katzcreates/Clean-Air-Necklace/3D Models/STLs/CleanAirNecklace_V2_ClearCoverChannel05.stl

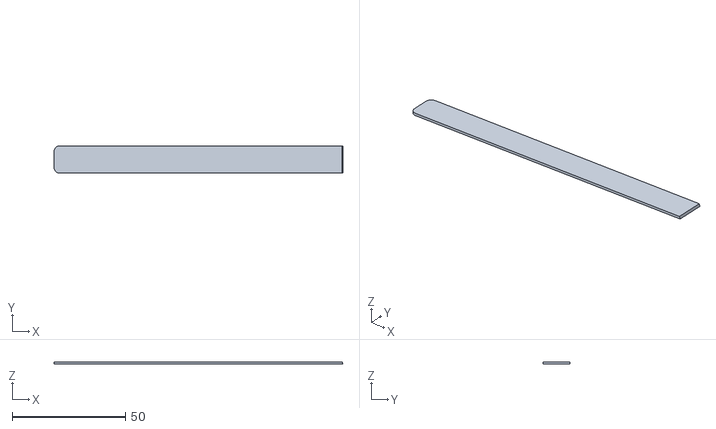
[picture p15: CAD file, 2023-09-17]
3D Models/STLs/CleanAirNecklace_V2_ClearCoverChannel05.stl
127.4 x 12.0 x 1.00
