katzcreates/Clean-Air-Necklace/3D Models/STLs/CleanAirNecklace_V2_ClearCoverChannel02.stl

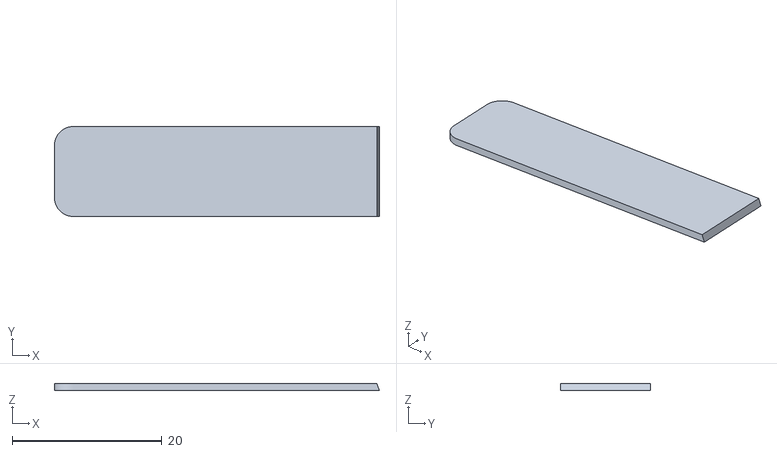
[picture p16: CAD file, 2023-09-17]
3D Models/STLs/CleanAirNecklace_V2_ClearCoverChannel02.stl
43.4 x 12.0 x 1.00
