katzcreates/Clean-Air-Necklace/3D Models/STLs/CleanAirNecklace_V2_LEDChannel01.stl

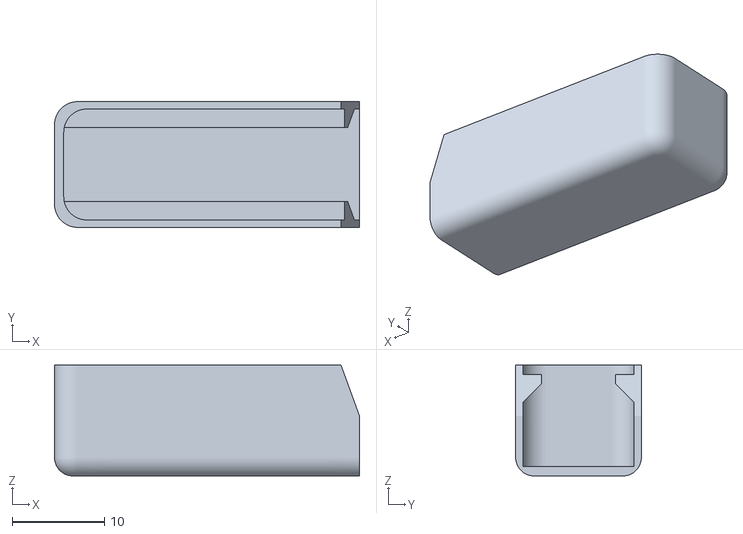
[picture p17: CAD file, 2023-09-17]
3D Models/STLs/CleanAirNecklace_V2_LEDChannel01.stl
33.0 x 13.6 x 12.0
