katzcreates/Clean-Air-Necklace/3D Models/STLs/CleanAirNecklace_V2_ClearCoverChannel03.stl

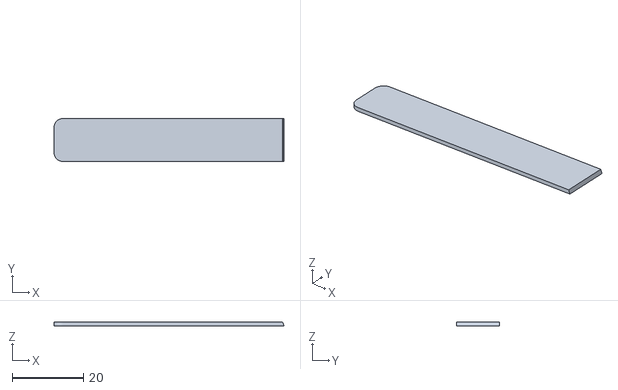
[picture p18: CAD file, 2023-09-17]
3D Models/STLs/CleanAirNecklace_V2_ClearCoverChannel03.stl
64.4 x 12.0 x 1.00
