katzcreates/Clean-Air-Necklace/3D Models/STLs/CleanAirNecklace_V2_ClearCoverChannel08.stl

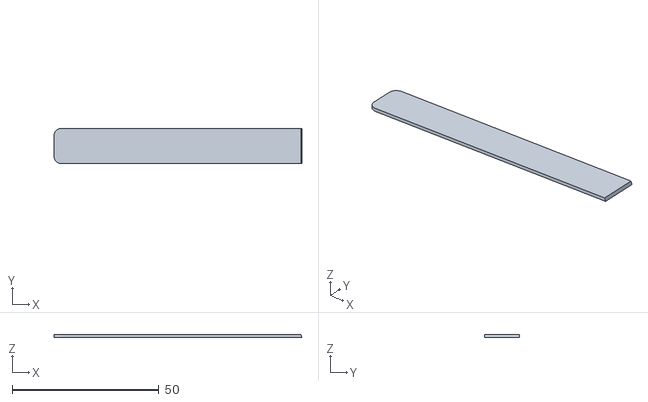
[picture p19: CAD file, 2023-09-17]
3D Models/STLs/CleanAirNecklace_V2_ClearCoverChannel08.stl
84.4 x 12.0 x 1.00
