katzcreates/Clean-Air-Necklace/3D Models/STLs/CleanAirNecklace_V2_LEDChannel08.stl

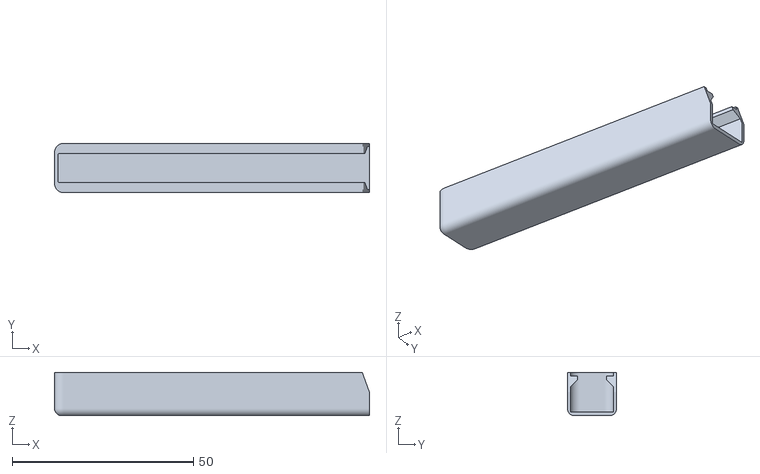
[picture p20: CAD file, 2023-09-17]
3D Models/STLs/CleanAirNecklace_V2_LEDChannel08.stl
87.0 x 13.6 x 12.0
