katzcreates/Clean-Air-Necklace/3D Models/STLs/CleanAirNecklace_V2_LEDChannel07.stl

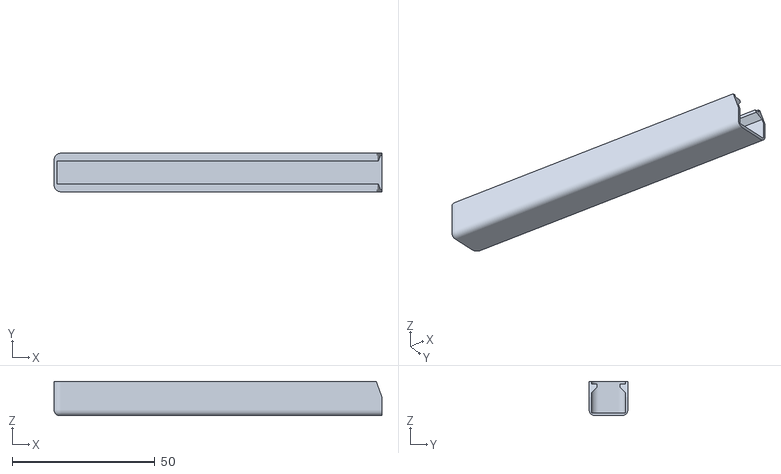
[picture p21: CAD file, 2023-09-17]
3D Models/STLs/CleanAirNecklace_V2_LEDChannel07.stl
115.0 x 13.6 x 12.0
