katzcreates/Clean-Air-Necklace/3D Models/STLs/CleanAirNecklace_V2_LEDChannel05.stl

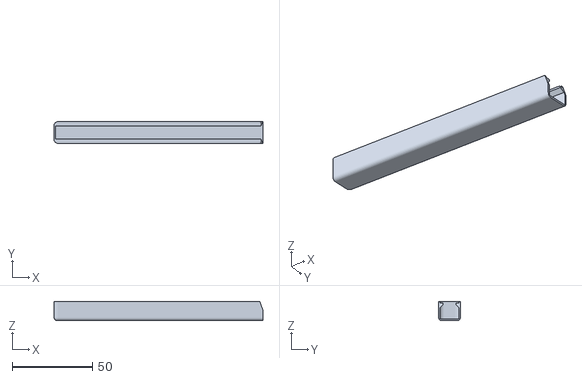
[picture p22: CAD file, 2023-09-17]
3D Models/STLs/CleanAirNecklace_V2_LEDChannel05.stl
130.0 x 13.6 x 12.0
