katzcreates/Clean-Air-Necklace/3D Models/STLs/CleanAirNecklace_V2_ClearCoverChannel06.stl

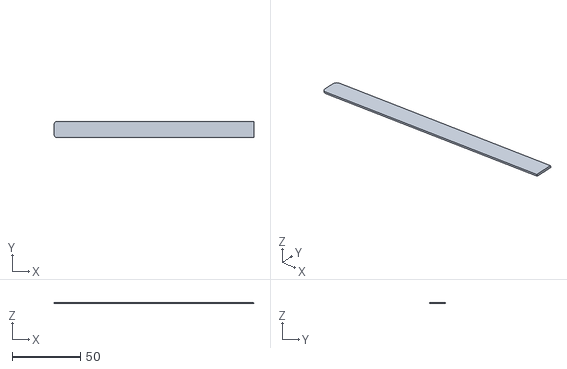
[picture p23: CAD file, 2023-09-17]
3D Models/STLs/CleanAirNecklace_V2_ClearCoverChannel06.stl
146.4 x 12.0 x 1.00
