katzcreates/Clean-Air-Necklace/3D Models/STLs/CleanAirNecklace_V2_MCUEnclosureDrop.stl

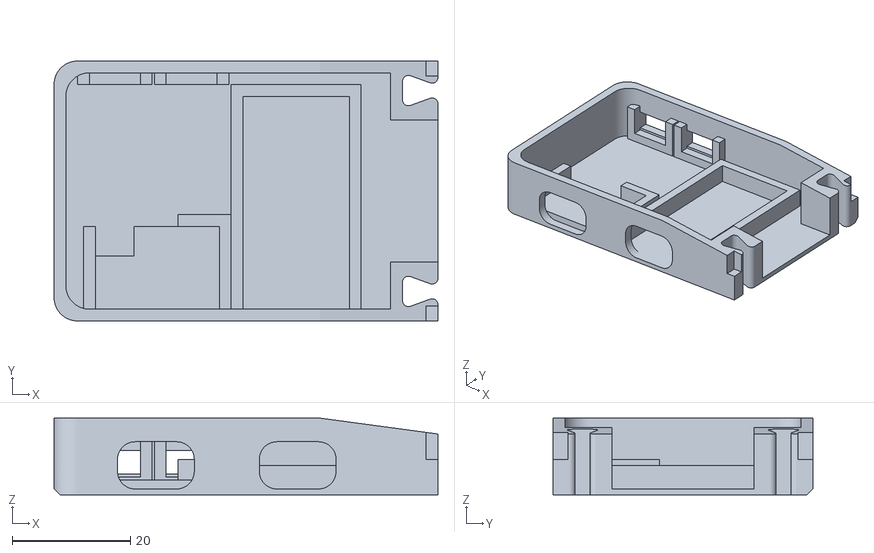
[picture p24: CAD file, 2023-09-17]
3D Models/STLs/CleanAirNecklace_V2_MCUEnclosureDrop.stl
65.0 x 44.0 x 13.0
