katzcreates/Clean-Air-Necklace/3D Models/STLs/CleanAirNecklace_V2_OpaqueCoverRight.stl

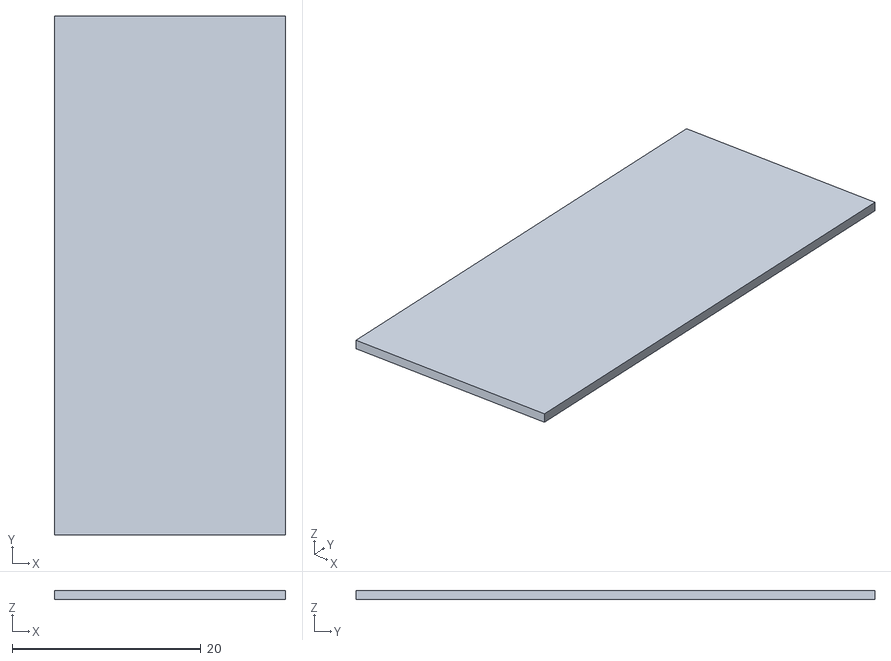
[picture p25: CAD file, 2023-09-17]
3D Models/STLs/CleanAirNecklace_V2_OpaqueCoverRight.stl
24.5 x 55.0 x 1.00
