katzcreates/Clean-Air-Necklace/3D Models/STLs/CleanAirNecklace_V2_LEDChannel02.stl

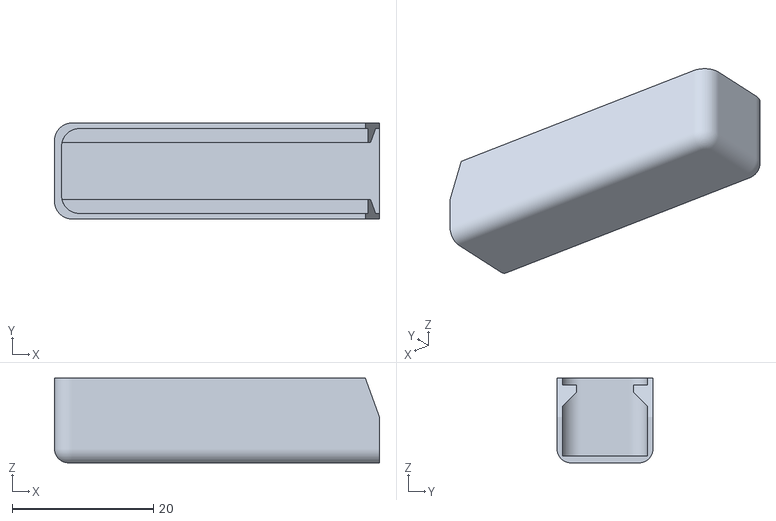
[picture p26: CAD file, 2023-09-17]
3D Models/STLs/CleanAirNecklace_V2_LEDChannel02.stl
46.0 x 13.6 x 12.0
