katzcreates/Clean-Air-Necklace/3D Models/STLs/CleanAirNecklace_V2_LEDChannel11.stl

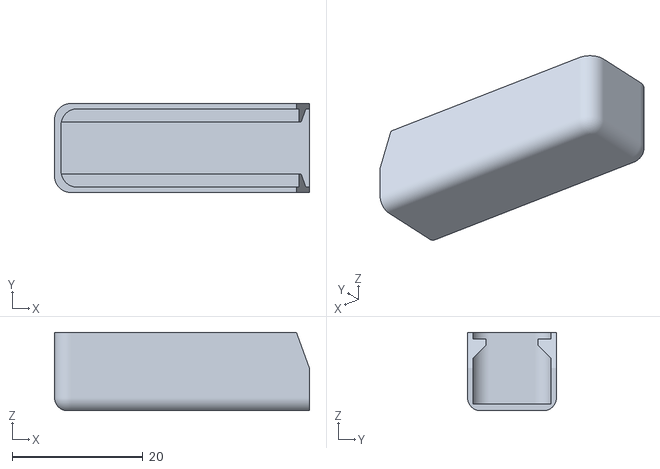
[picture p27: CAD file, 2023-09-17]
3D Models/STLs/CleanAirNecklace_V2_LEDChannel11.stl
39.0 x 13.6 x 12.0
