katzcreates/Clean-Air-Necklace/3D Models/STLs/CleanAirNecklace_V2_LEDChannel09.stl

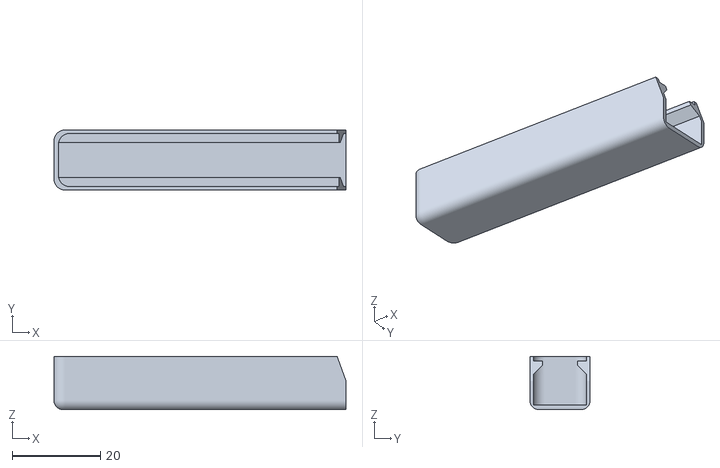
[picture p28: CAD file, 2023-09-17]
3D Models/STLs/CleanAirNecklace_V2_LEDChannel09.stl
66.0 x 13.6 x 12.0
