katzcreates/Clean-Air-Necklace/3D Models/STLs/CleanAirNecklace_V2_ClearCover.stl

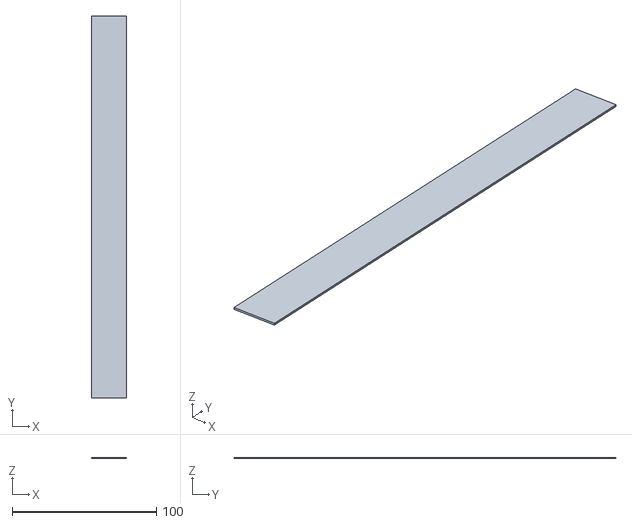
[picture p32: CAD file, 2023-09-17]
3D Models/STLs/CleanAirNecklace_V2_ClearCover.stl
24.5 x 265.0 x 1.00
