katzcreates/Clean-Air-Necklace/3D Models/STLs/ESDK_SensorAddOnPantClip.stl

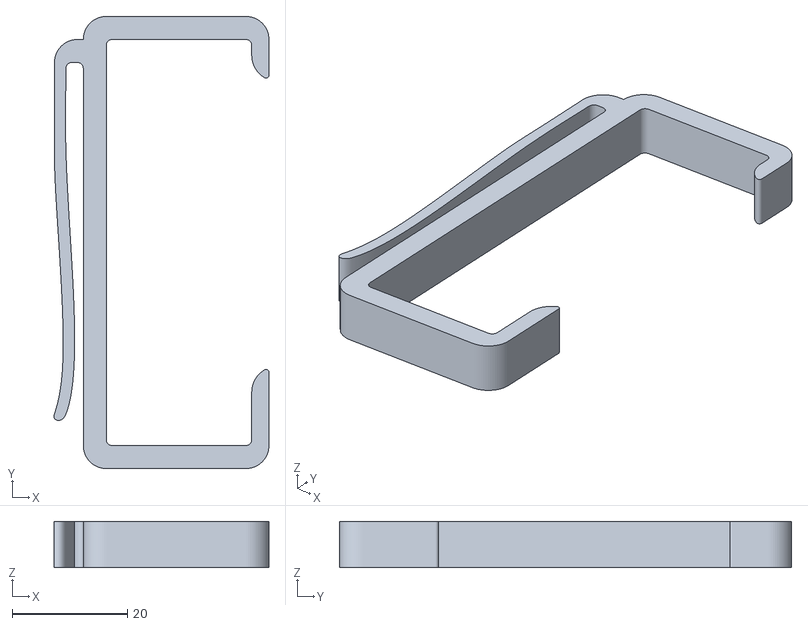
[picture p34: CAD file, 2022-03-12]
3D Models/STLs/ESDK_SensorAddOnPantClip.stl
37.3 x 78.5 x 8.00
