katzcreates/Clean-Air-Necklace/3D Models/STLs/ESDK_SensorAddOnBeltClip.stl

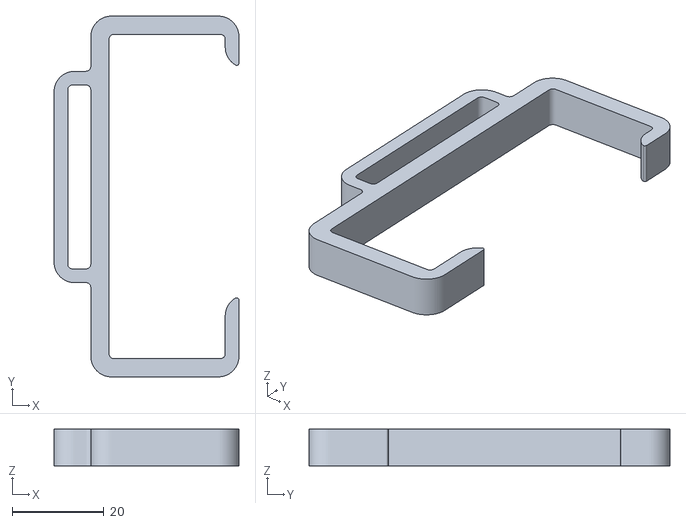
[picture p35: CAD file, 2022-03-12]
3D Models/STLs/ESDK_SensorAddOnBeltClip.stl
40.2 x 78.5 x 8.00
