katzcreates/Clean-Air-Necklace/3D Models/STLs/CleanAirNecklace_CircumferenceExtender.stl

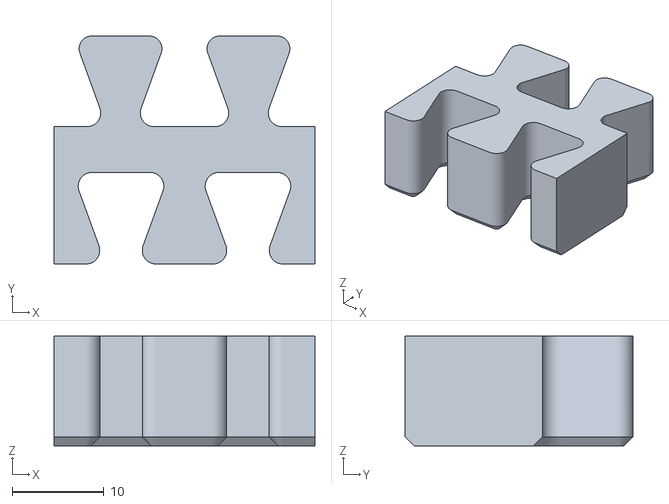
[picture p36: CAD file, 2022-03-12]
3D Models/STLs/CleanAirNecklace_CircumferenceExtender.stl
28.5 x 24.9 x 12.0
